jkx/DIY-Wireless-Bug/hardware/shields/sensor_shield/v2/sensor_shield.png

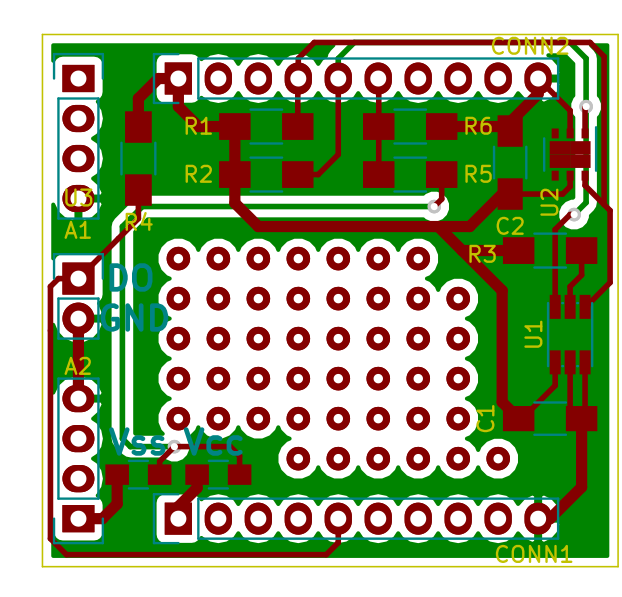
hardware/shields/sensor_shield/v2/sensor_shield.png
