jkx/DIY-Wireless-Bug/hardware/bugOne/mini/bugOne_mini.pcb.png

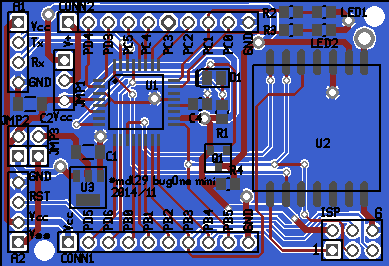
hardware/bugOne/mini/bugOne_mini.pcb.png
