jkx/DIY-Wireless-Bug/hardware/bugOne/mini/bugOne_mini.sch.png

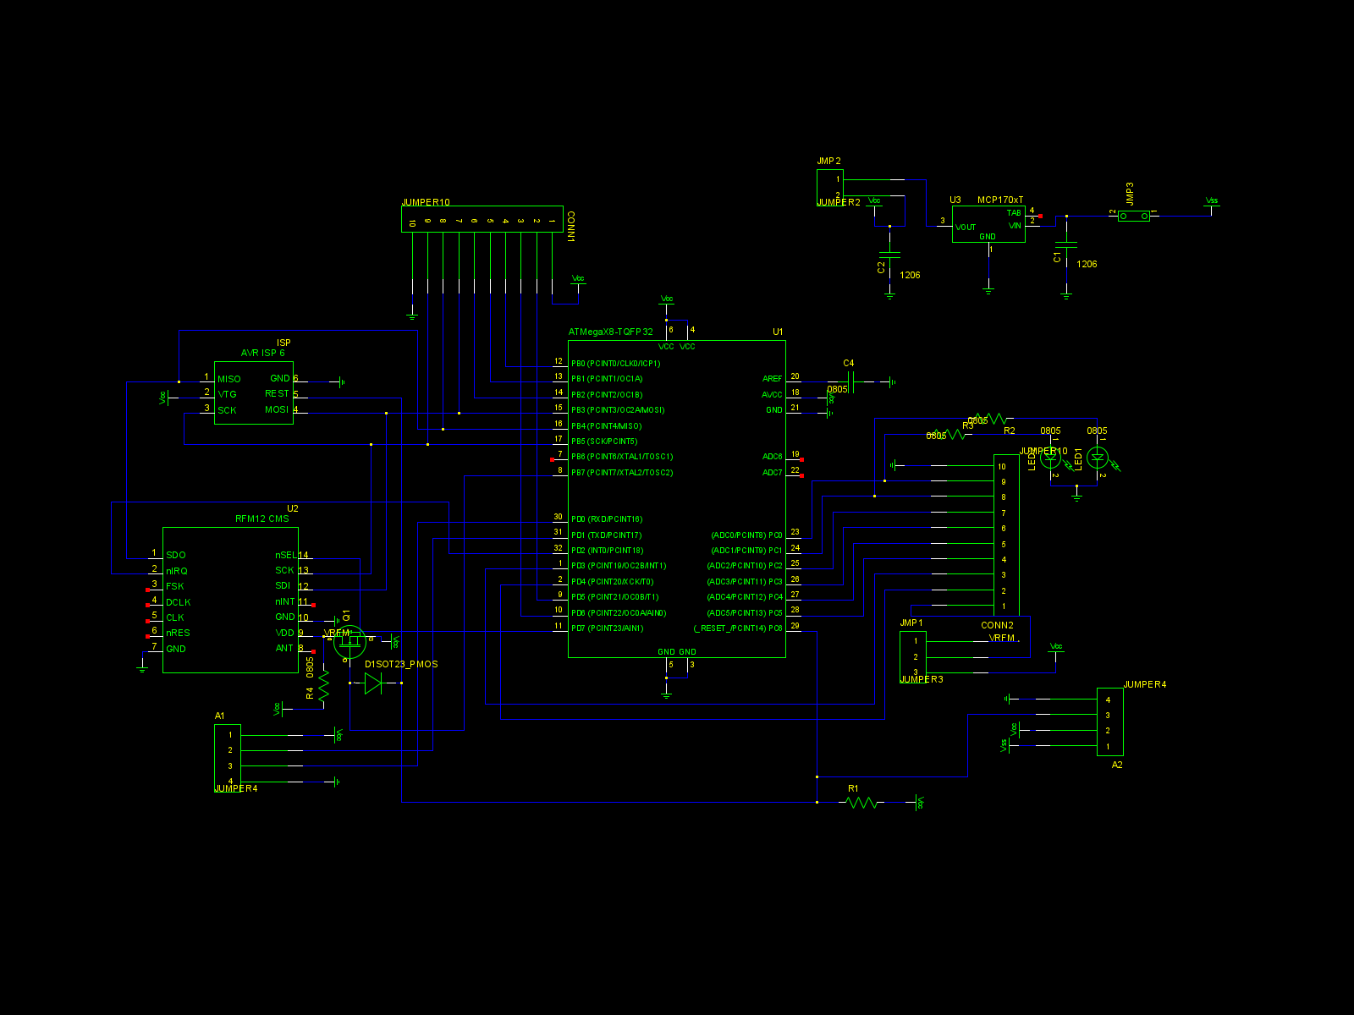
hardware/bugOne/mini/bugOne_mini.sch.png
