jkx/DIY-Wireless-Bug/software/projects/enc28j60/dnslkup.c

/*********************************************
 * vim:sw=8:ts=8:si:et
 * To use the above modeline in vim you must have "set modeline" in your .vimrc
 * Author: Guido Socher
 * Copyright:LGPL V2
 * See http://www.gnu.org/licenses/old-licenses/lgpl-2.0.html
 *
 * DNS look-up functions based on the udp client
 *
 *********************************************/
#include <avr/io.h>
// http://www.nongnu.org/avr-libc/changes-1.8.html:
#define __PROG_TYPES_COMPAT__
#include <avr/pgmspace.h>
#include <string.h>
#include <ctype.h>
#include <stdlib.h>
#include "net.h"
#include "enc28j60.h"
#include "ip_arp_udp_tcp.h"
#include "ip_config.h"

#ifndef UDP_client
#error "ERROR: you need to enable UDP_client support in ip_config.h to use the DNS look-up"
#endif

static uint8_t dnstid_l=0; // a counter for transaction ID
// src port high byte must be a a0 or higher:
#define DNSCLIENT_SRC_PORT_H 0xe0 
uint8_t dnsip[4]={1,2,3,4}; // the google public DNS, don't change unless there is a real need
static uint8_t haveDNSanswer=0;
static uint8_t dns_answerip[4];
static uint8_t dns_ansError=0;


uint8_t dnslkup_haveanswer(void)
{       
        return(haveDNSanswer);
}

uint8_t dnslkup_get_error_info(void)
{       
        return(dns_ansError);
}

// ip is the return value
void dnslkup_get_ip(uint8_t *ip)
{       
        uint8_t i=0;
        while(i<4){ip[i]=dns_answerip[i];i++;}
}

// Determine if the string is a hostname or an IP address
// A valid IP is e.g. "10.0.11.22"
uint8_t string_is_ipv4(const char *str){
        uint8_t previous_char_was_digit=0;
        uint8_t dotcnt=0;
        while(*str){
                if (isdigit(*str)){
                        previous_char_was_digit=1;
                }else if (*str=='.' && previous_char_was_digit==1){
                        previous_char_was_digit=0;
                        dotcnt++;
                }else{
                        return(0); // any other char: not an IP
                }
                str++;
        }
        if (previous_char_was_digit==1 && dotcnt==3){
                return(1); // ok looks like a numeric IP
        }
        return(0); // not an IP: did not end in a digit
}

// send a DNS udp request packet
// See http://www.ietf.org/rfc/rfc1034.txt 
// and http://www.ietf.org/rfc/rfc1035.txt
// gwmac is the internal mac addess of your router
// because we use 8.8.8.8 as a DNS server
uint8_t dnslkup_request(uint8_t *buf,const char *hostname,const uint8_t *gwmac)
{
        uint8_t i,lenpos,lencnt;
        haveDNSanswer=0;
        if(!enc28j60linkup()){
                dns_ansError=4; // could not send request, link down
                return(1);
        }
        dns_ansError=0;
        dnstid_l++; // increment for next request, finally wrap
        send_udp_prepare(buf,(DNSCLIENT_SRC_PORT_H<<8)|(dnstid_l&0xff),dnsip,53,gwmac);
        // fill tid:
        //buf[UDP_DATA_P] see below
        buf[UDP_DATA_P+1]=dnstid_l;
        buf[UDP_DATA_P+2]=1; // flags, standard recursive query
        i=3;
        // most fields are zero, here we zero everything and fill later
        while(i<12){ 
                buf[UDP_DATA_P+i]=0;
                i++;
        }
        buf[UDP_DATA_P+5]=1; // 1 question
        // the structure of the domain name
        // we ask for is always length, string, length, string, ...
        // for earch portion of the name.
        // www.twitter.com would become: 3www7twitter3com
        // 
        // the first len starts at i=12
        lenpos=12;
        i=13;
        lencnt=1; // need to start with one as there is no dot before the domain name and the below algorithm assumes lencnt=0 at dot
        while(*hostname){
                if (*hostname=='\0') break;
                if (*hostname=='.'){
                        buf[UDP_DATA_P+lenpos]=lencnt-1; // fill the length field
                        lencnt=0;
                        lenpos=i;
                }
                buf[UDP_DATA_P+i]=*hostname;
                lencnt++;
                i++;
                hostname++;
        }
        buf[UDP_DATA_P+lenpos]=lencnt-1;
        buf[UDP_DATA_P+i]=0; // terminate with zero, means root domain.
        i++;
        buf[UDP_DATA_P+i]=0;
        i++;
        buf[UDP_DATA_P+i]=1; // type A
        i++;
        buf[UDP_DATA_P+i]=0; 
        i++;
        buf[UDP_DATA_P+i]=1; // class IN
        i++;
        // we encode the length into the upper byte of the TID
        // this way we can easily jump over the query section
        // of the answer:
        buf[UDP_DATA_P]=i-12;
        send_udp_transmit(buf,i);
        return(0);
}

// process the answer from the dns server:
// return 1 on sucessful processing of answer.
// We set also the variable haveDNSanswer
uint8_t udp_client_check_for_dns_answer(uint8_t *buf,uint16_t plen){
        uint8_t j,i;
        if (plen<70){
                return(0);
        }
        if (buf[UDP_SRC_PORT_L_P]!=53){
                // not from a DNS
                return(0);
        }
        if (buf[UDP_DST_PORT_H_P]!=DNSCLIENT_SRC_PORT_H){ 
                return(0);
        }
        // we use the TID also as port:
        if (buf[UDP_DST_PORT_L_P]!=dnstid_l){ 
                return(0);
        }
        /* we can skip this check, it is quite unlikely that we
         * get a packet with the right tid from a DNS. Save some 
         * processing:
        // is the packet for my IP:
        if(eth_type_is_ip_and_my_ip(buf,plen)==0){
                return(0);
        }
        */
        if (buf[UDP_DATA_P+1]!=dnstid_l){ 
                return(0);
        }
        // check flags lower byte:
        if ((buf[UDP_DATA_P+3]&0x8F)!=0x80){ 
                // there is an error or server does not support recursive
                // queries. We can only work with servers that support recursive
                // queries.
                dns_ansError=1;
                return(0);
        }
        // there might be multiple answers, we use only the first one
        //
        // UDP_DATA_P+12+querylen is first byte of first answer.
        // The answer contains again the domain name and we need to
        // jump over it to find the IP. This part can be abbreviated by
        // the use of 2 byte pointers. See RFC 1035.
        i=12+buf[UDP_DATA_P]; // we encoded the query len into tid
ChecNextResp:
        if (buf[UDP_DATA_P+i] & 0xc0){
                // pointer
                i+=2;
        }else{
                // we just search for the first, zero=root domain
                // all other octets must be non zero
                while(i<plen-UDP_DATA_P-7){
                        i++;
                        if (buf[UDP_DATA_P+i]==0){
                                i++;
                                break;
                        }
                }
        }
        // There might be multipe records in the answer. 
        // We are searching for an A record (contains IP).
        // Contributed by Andras Tucsni
        if (buf[UDP_DATA_P+i+1] != 1){    // check type == 1 for "A"
                i += 2 + 2 + 4;    // skip type & class & TTL
                i += buf[UDP_DATA_P+i+1] + 2;    // skip datalength bytes
                if (i < plen-UDP_DATA_P-7){
                        goto ChecNextResp;
                }
                dns_ansError=3; // no A record found but packet ends 
                return(0);
        } 
        // We have an A record
        // i is now pointing to the high octet of the type field
        if (buf[UDP_DATA_P+i+9] !=4 ){
                dns_ansError=2; // not IPv4
                return(0);
        }
        i+=10;
        j=0;
        while(j<4){
                dns_answerip[j]=buf[UDP_DATA_P+i+j];
                j++;
        }
        haveDNSanswer=1;
        return(1);
}

/* end of dnslkup.c */
