jkx/DIY-Wireless-Bug/software/projects/test/main.c

/* 
   bugOne wireless test
   ====================
   - register the base bugOne functions : leds

 */ 


#include "bugOne.h"
#include <stdlib.h>
#include "config.h"

// include devices
#include "led.h"
#include "bandgap.h"


application_t applications[] = {
 {bandgap_init,bandgap_get,NULL,NULL},
 {NULL,led_get,led_set,NULL},
 {NULL,NULL,NULL,NULL}
};
